SadeepRathnayaka/Turbobot-Autonomous-Robot/turbobot_description/photos/DeskPortraitA_01.jpg

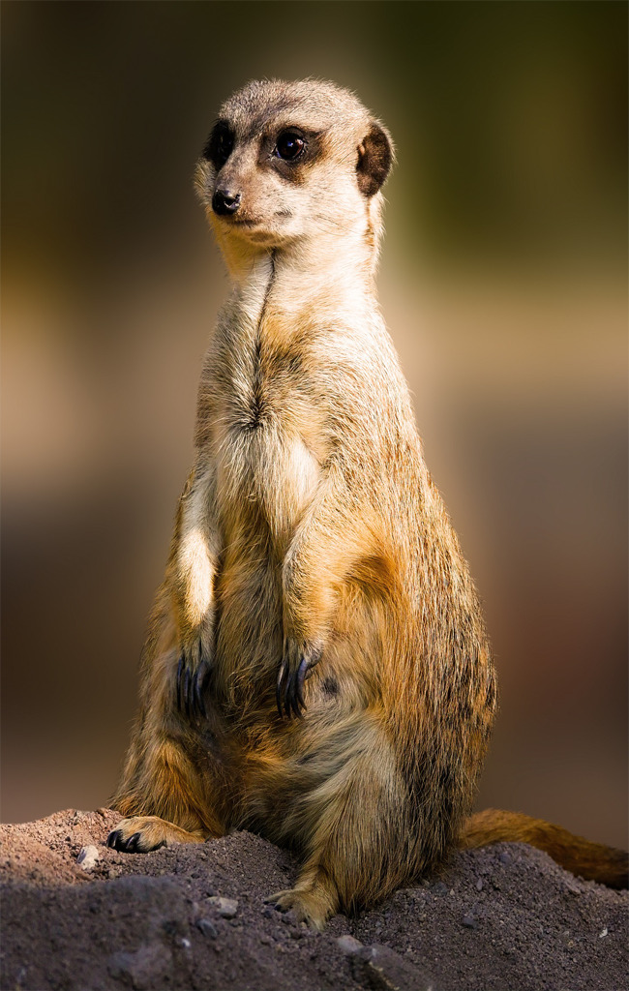
turbobot_description/photos/DeskPortraitA_01.jpg
