SadeepRathnayaka/Turbobot-Autonomous-Robot/turbobot_description/photos/DeskPortraitA_02.jpg

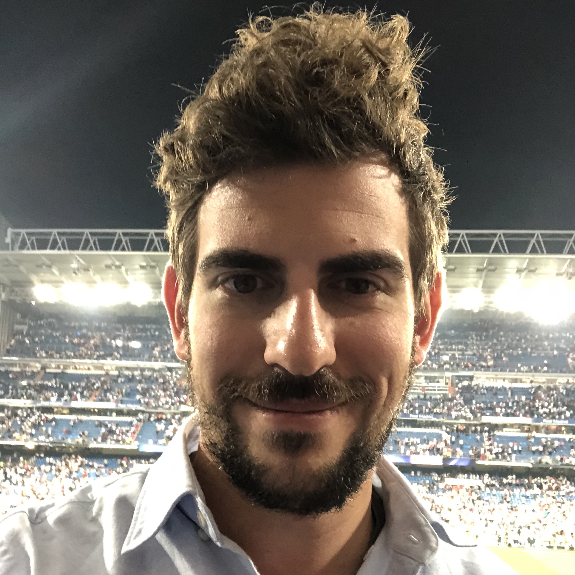
turbobot_description/photos/DeskPortraitA_02.jpg
