SadeepRathnayaka/Turbobot-Autonomous-Robot/turbobot_description/photos/DeskPortraitB_01.jpg

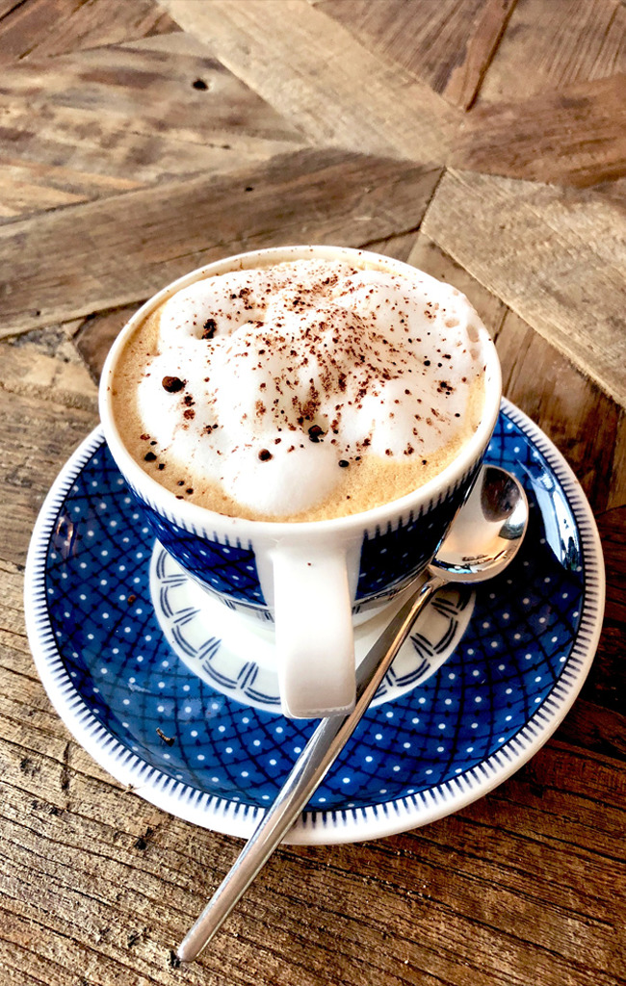
turbobot_description/photos/DeskPortraitB_01.jpg
