SadeepRathnayaka/Turbobot-Autonomous-Robot/turbobot_description/photos/DeskPortraitC_02.jpg

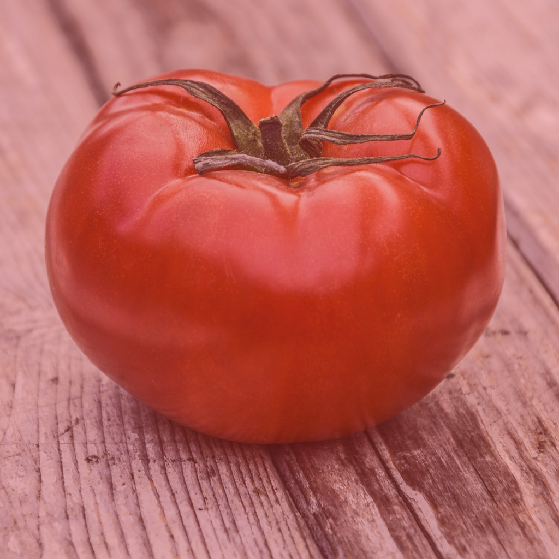
turbobot_description/photos/DeskPortraitC_02.jpg
