SadeepRathnayaka/Turbobot-Autonomous-Robot/turbobot_description/photos/DeskPortraitD_01.jpg

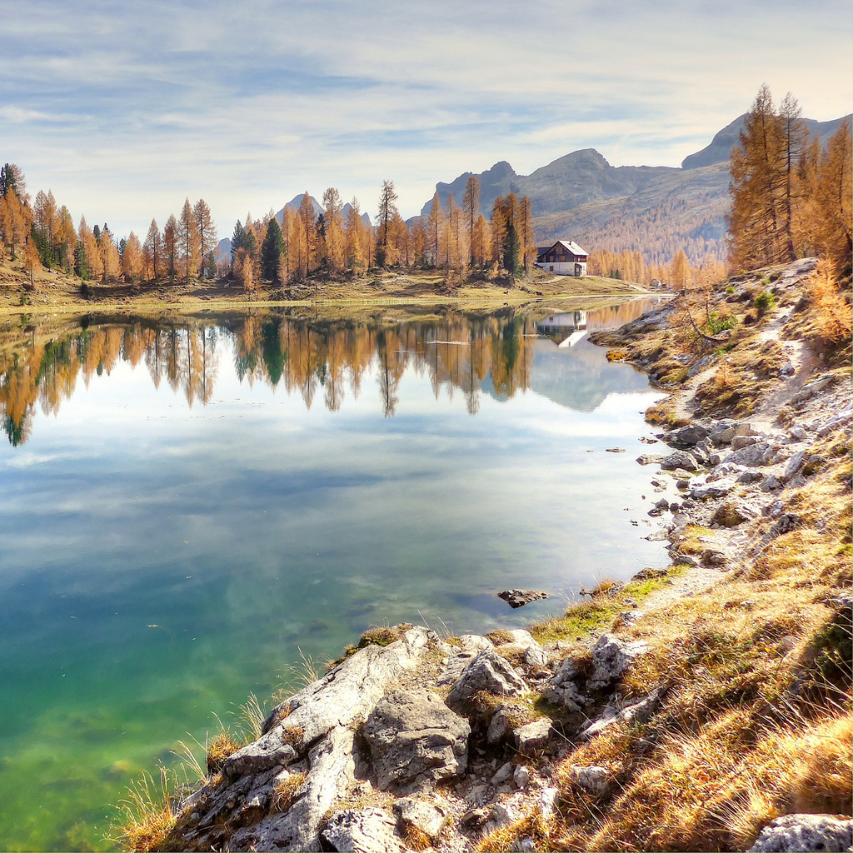
turbobot_description/photos/DeskPortraitD_01.jpg
