SadeepRathnayaka/Turbobot-Autonomous-Robot/turbobot_description/photos/DeskPortraitD_04.jpg

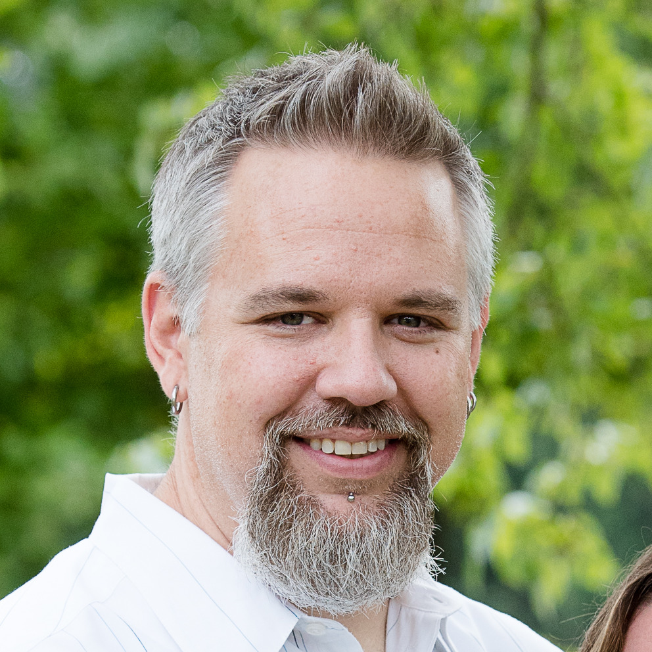
turbobot_description/photos/DeskPortraitD_04.jpg
