SadeepRathnayaka/Turbobot-Autonomous-Robot/turbobot_description/photos/PortraitA_01.jpg

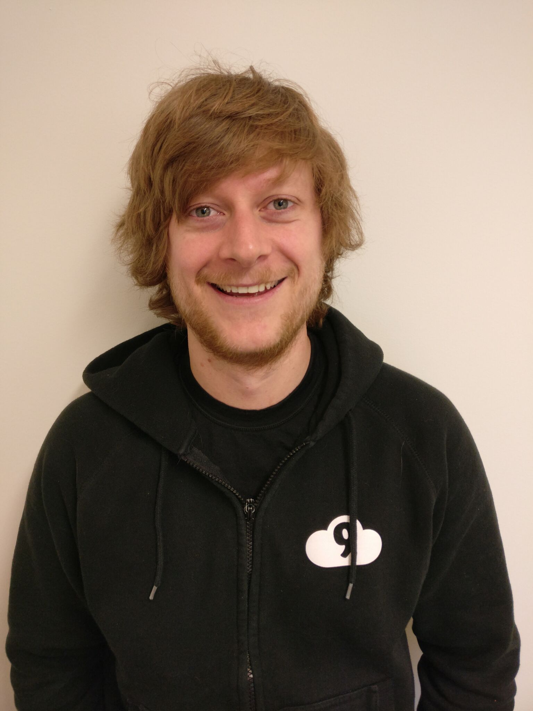
turbobot_description/photos/PortraitA_01.jpg
