SadeepRathnayaka/Turbobot-Autonomous-Robot/turbobot_description/photos/PortraitA_02.jpg

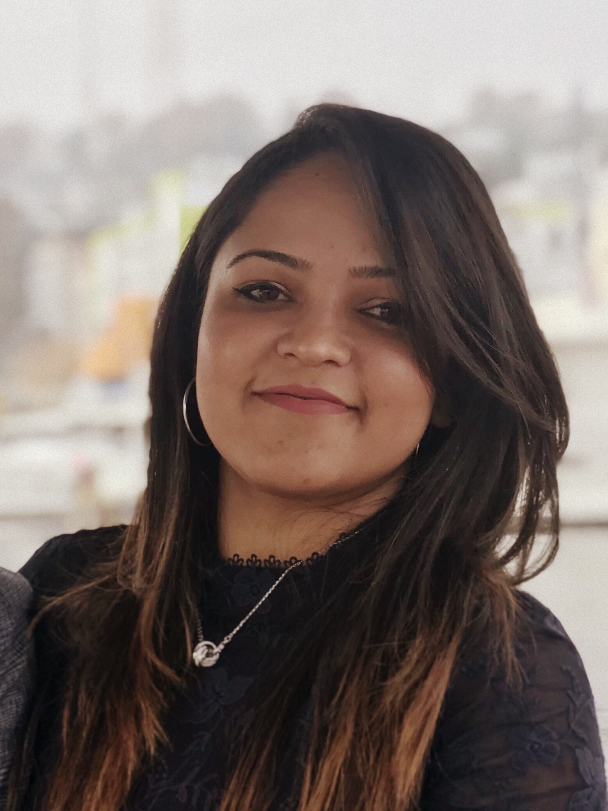
turbobot_description/photos/PortraitA_02.jpg
