SadeepRathnayaka/Turbobot-Autonomous-Robot/turbobot_description/photos/PortraitB_01.jpg

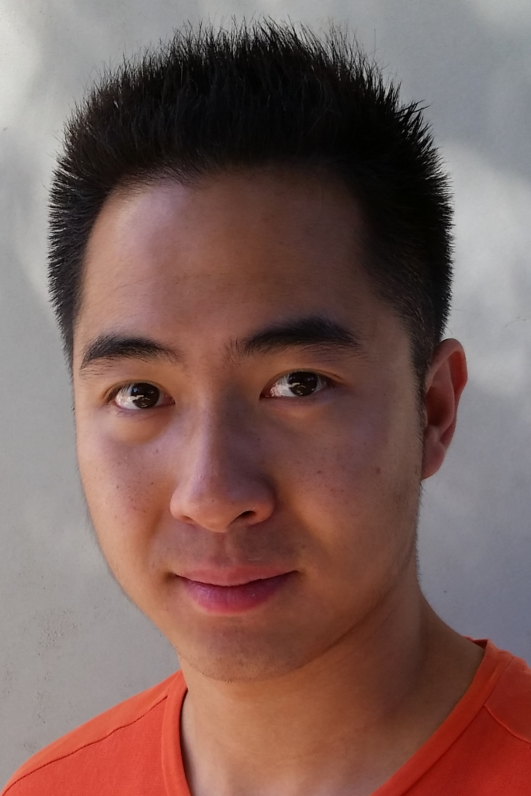
turbobot_description/photos/PortraitB_01.jpg
