SadeepRathnayaka/Turbobot-Autonomous-Robot/turbobot_description/photos/PortraitB_02.jpg

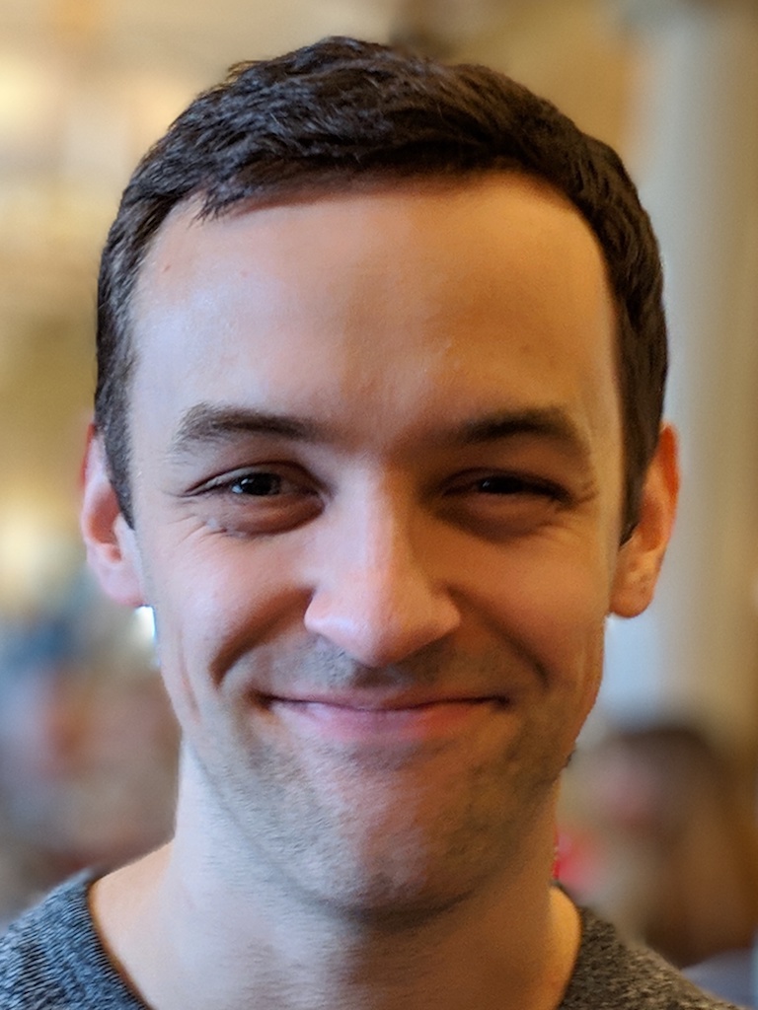
turbobot_description/photos/PortraitB_02.jpg
