SadeepRathnayaka/Turbobot-Autonomous-Robot/turbobot_description/photos/PortraitB_03.jpg

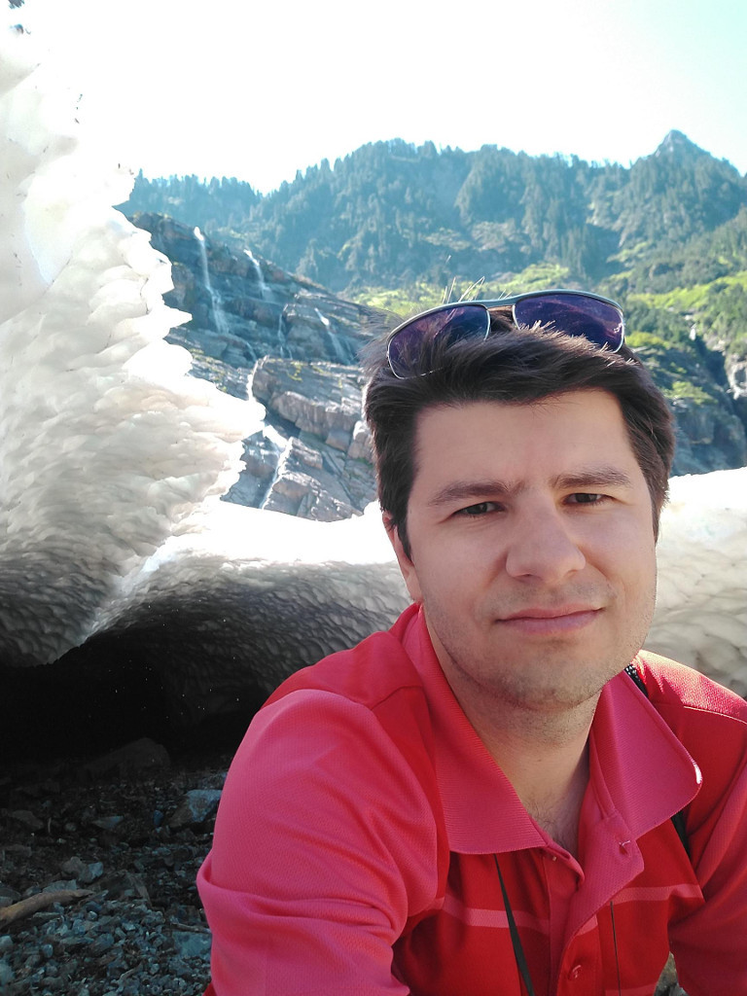
turbobot_description/photos/PortraitB_03.jpg
