SadeepRathnayaka/Turbobot-Autonomous-Robot/turbobot_description/photos/PortraitC_01.jpg

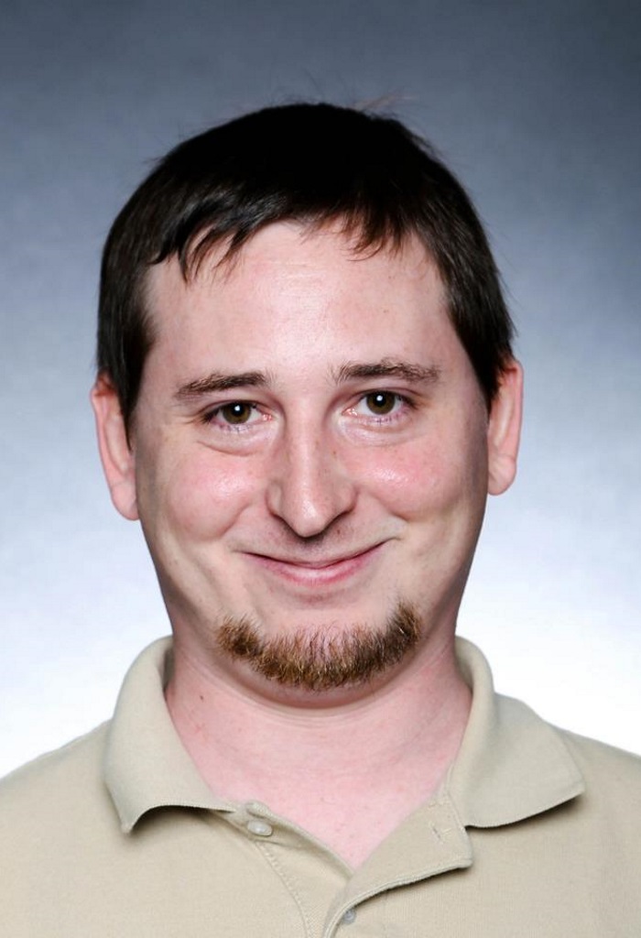
turbobot_description/photos/PortraitC_01.jpg
