SadeepRathnayaka/Turbobot-Autonomous-Robot/turbobot_description/photos/PortraitD_01.jpg

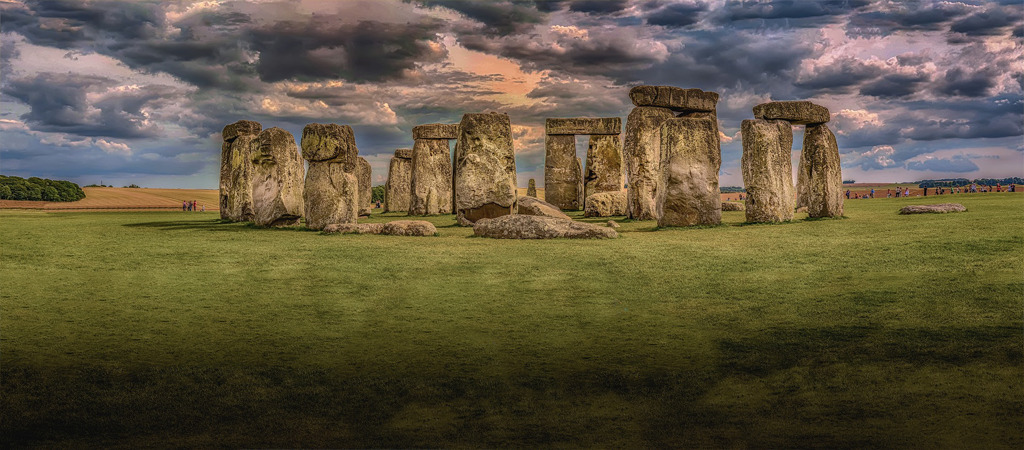
turbobot_description/photos/PortraitD_01.jpg
