SadeepRathnayaka/Turbobot-Autonomous-Robot/turbobot_description/photos/PortraitE_01.jpg

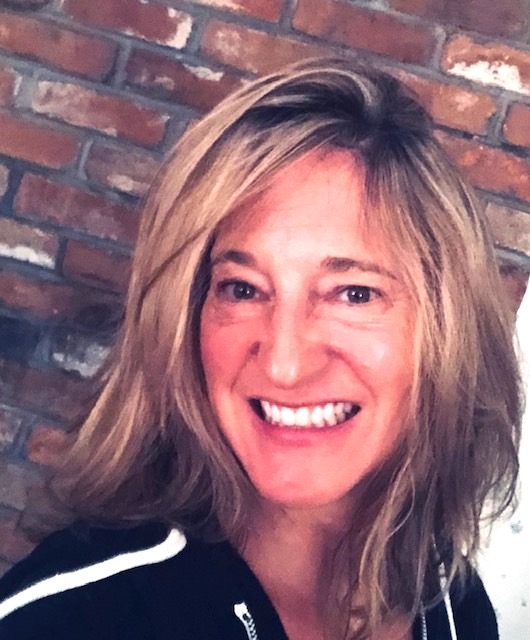
turbobot_description/photos/PortraitE_01.jpg
