SadeepRathnayaka/Turbobot-Autonomous-Robot/turbobot_description/photos/PortraitE_02.jpg

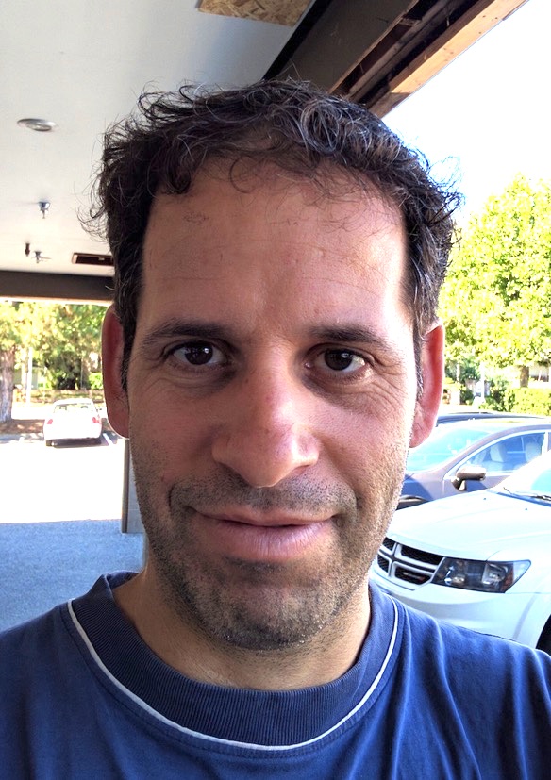
turbobot_description/photos/PortraitE_02.jpg
