SadeepRathnayaka/Turbobot-Autonomous-Robot/turbobot_description/models/aws_robomaker_residential_Ball_01/materials/textures/aws_Ball_01.png

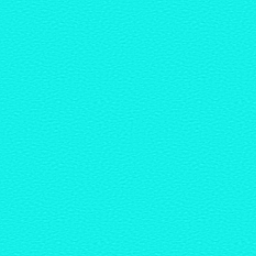
turbobot_description/models/aws_robomaker_residential_Ball_01/materials/textures/aws_Ball_01.png
