SadeepRathnayaka/Turbobot-Autonomous-Robot/turbobot_description/models/aws_robomaker_residential_Bed_01/materials/textures/aws_Bed_01.png

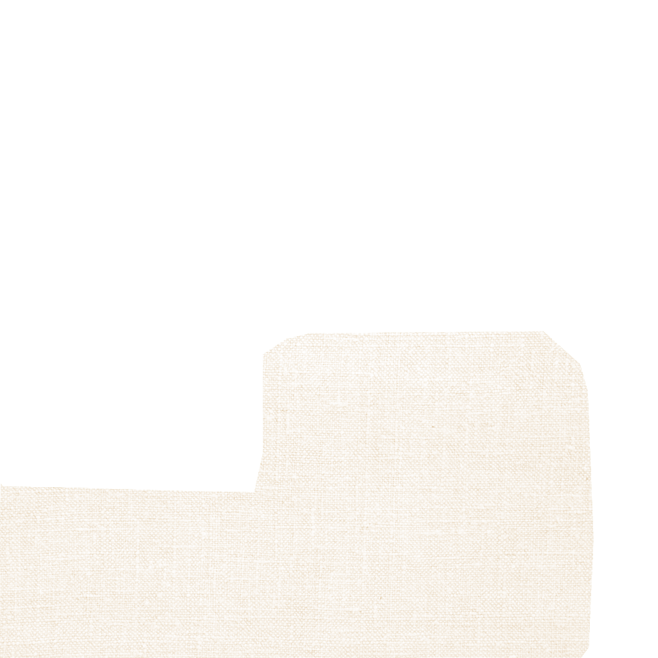
turbobot_description/models/aws_robomaker_residential_Bed_01/materials/textures/aws_Bed_01.png
