SadeepRathnayaka/Turbobot-Autonomous-Robot/turbobot_description/models/aws_robomaker_residential_Board_01/materials/textures/aws_Board_01.png

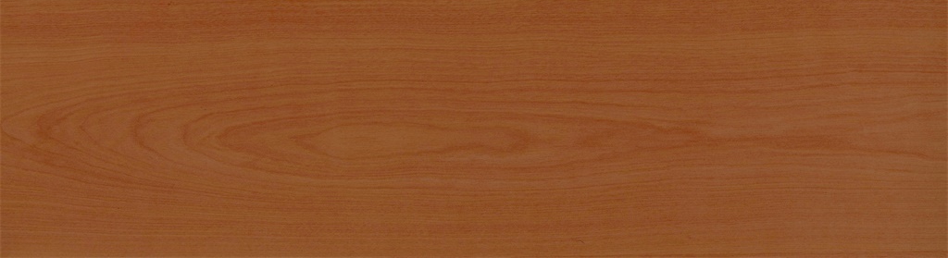
turbobot_description/models/aws_robomaker_residential_Board_01/materials/textures/aws_Board_01.png
