SadeepRathnayaka/Turbobot-Autonomous-Robot/turbobot_description/models/aws_robomaker_residential_ChairA_01/materials/textures/aws_ChairA_01.png

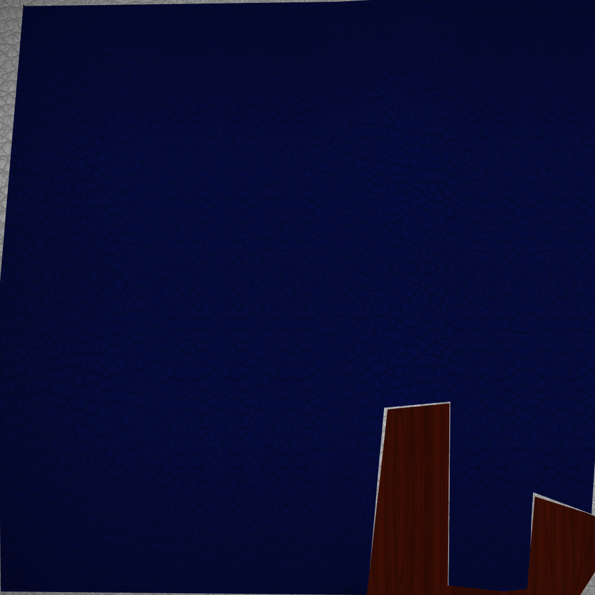
turbobot_description/models/aws_robomaker_residential_ChairA_01/materials/textures/aws_ChairA_01.png
