SadeepRathnayaka/Turbobot-Autonomous-Robot/turbobot_description/models/aws_robomaker_residential_Chandelier_01/materials/textures/aws_Chandelier_01.png

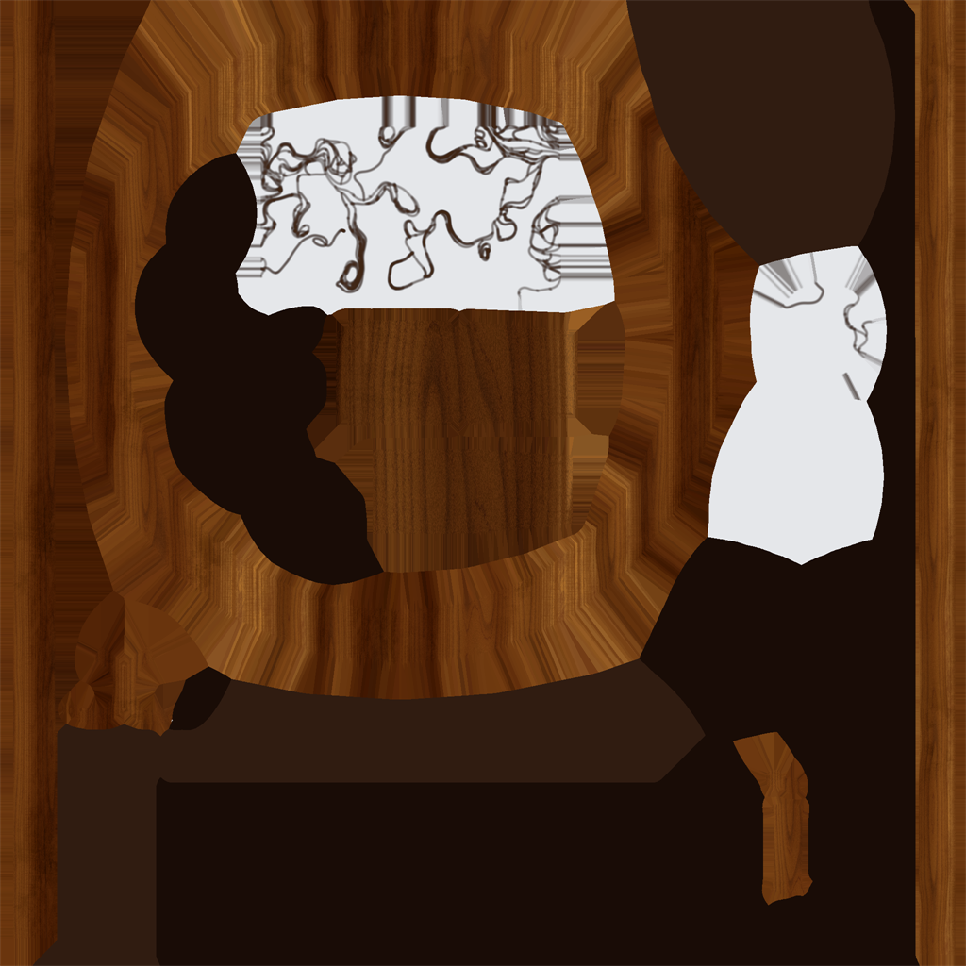
turbobot_description/models/aws_robomaker_residential_Chandelier_01/materials/textures/aws_Chandelier_01.png
