SadeepRathnayaka/Turbobot-Autonomous-Robot/turbobot_description/models/aws_robomaker_residential_CookingBench_01/materials/textures/aws_CookingBench_01.png

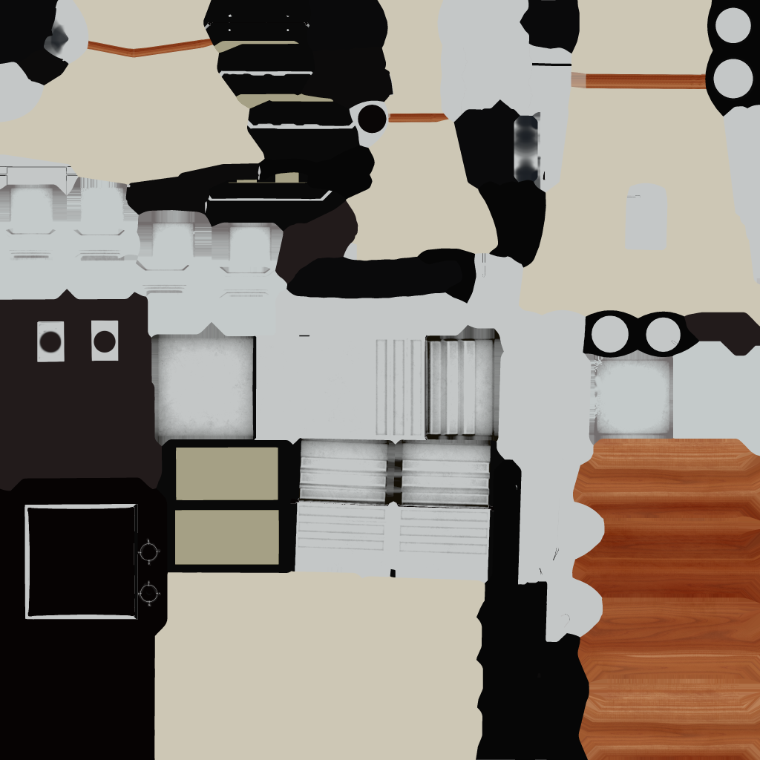
turbobot_description/models/aws_robomaker_residential_CookingBench_01/materials/textures/aws_CookingBench_01.png
