SadeepRathnayaka/Turbobot-Autonomous-Robot/turbobot_description/models/aws_robomaker_residential_Curtain_01/materials/textures/aws_Curtain_01.png

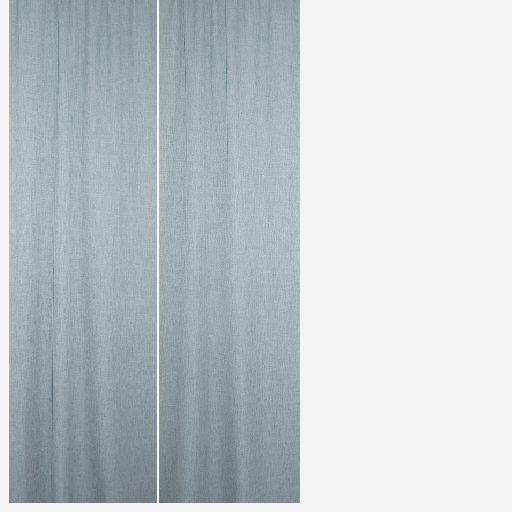
turbobot_description/models/aws_robomaker_residential_Curtain_01/materials/textures/aws_Curtain_01.png
