SadeepRathnayaka/Turbobot-Autonomous-Robot/turbobot_description/models/aws_robomaker_residential_Door_01/materials/textures/aws_Door_01.png

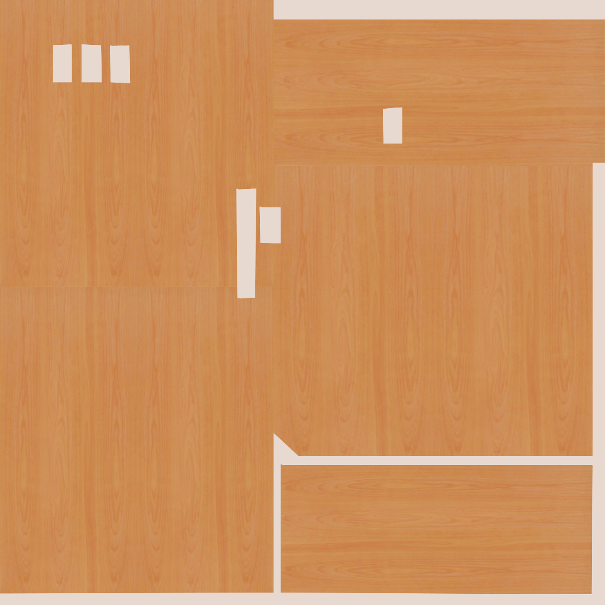
turbobot_description/models/aws_robomaker_residential_Door_01/materials/textures/aws_Door_01.png
