SadeepRathnayaka/Turbobot-Autonomous-Robot/turbobot_description/models/aws_robomaker_residential_FloorB_01/materials/textures/aws_FloorB_01.png

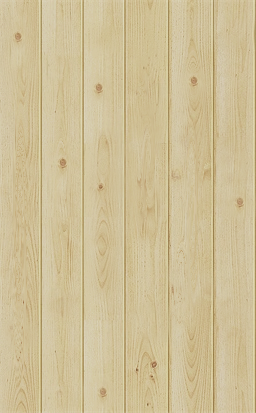
turbobot_description/models/aws_robomaker_residential_FloorB_01/materials/textures/aws_FloorB_01.png
