SadeepRathnayaka/Turbobot-Autonomous-Robot/turbobot_description/models/aws_robomaker_residential_Handle_01/materials/textures/aws_Handle_01.png

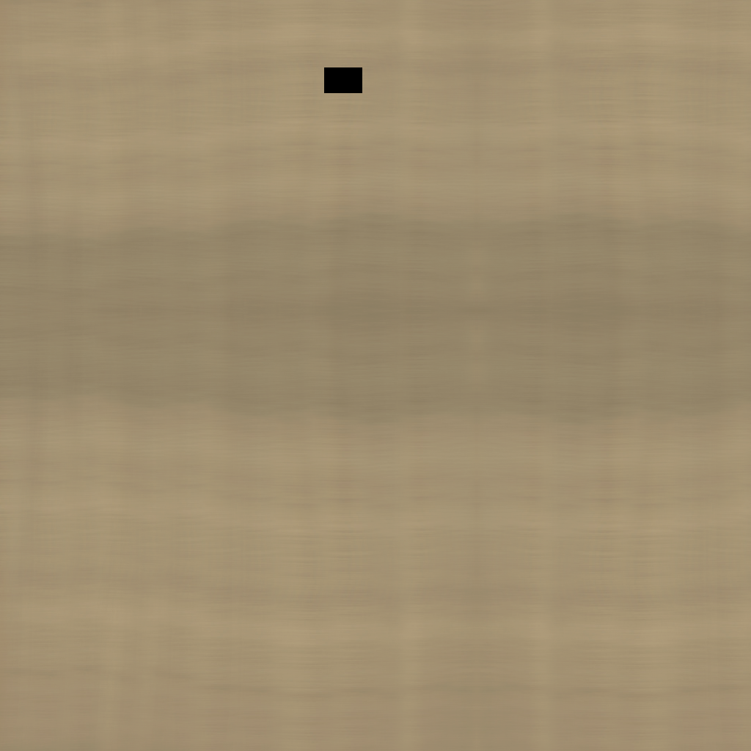
turbobot_description/models/aws_robomaker_residential_Handle_01/materials/textures/aws_Handle_01.png
