SadeepRathnayaka/Turbobot-Autonomous-Robot/turbobot_description/models/aws_robomaker_residential_NightStand_01/materials/textures/aws_NightStand_01.png

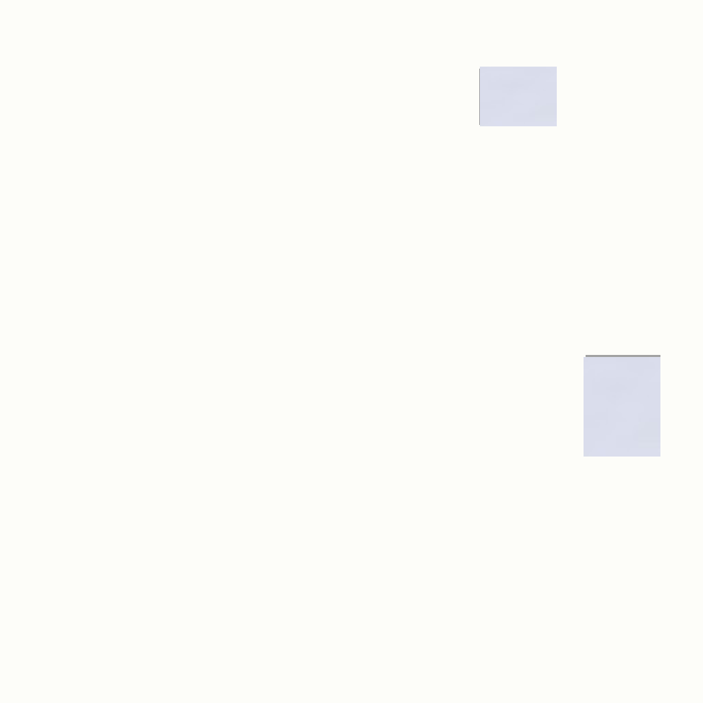
turbobot_description/models/aws_robomaker_residential_NightStand_01/materials/textures/aws_NightStand_01.png
