SadeepRathnayaka/Turbobot-Autonomous-Robot/turbobot_description/models/aws_robomaker_residential_PortraitA_01/materials/textures/aws_PortraitA_02.png

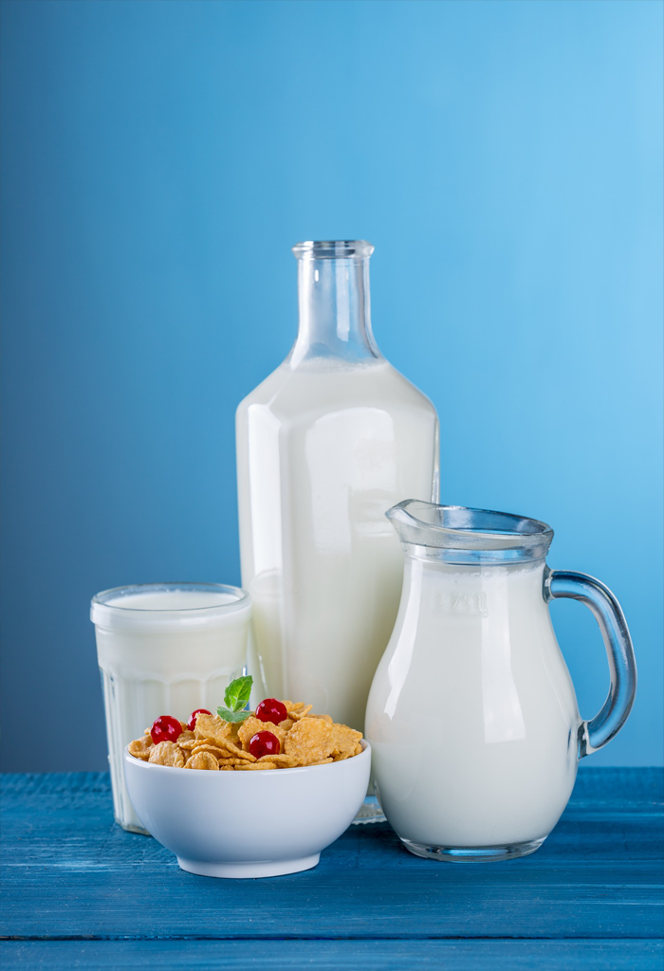
turbobot_description/models/aws_robomaker_residential_PortraitA_01/materials/textures/aws_PortraitA_02.png
