SadeepRathnayaka/Turbobot-Autonomous-Robot/turbobot_description/models/aws_robomaker_residential_PortraitB_01/materials/textures/aws_PortraitB_02.png

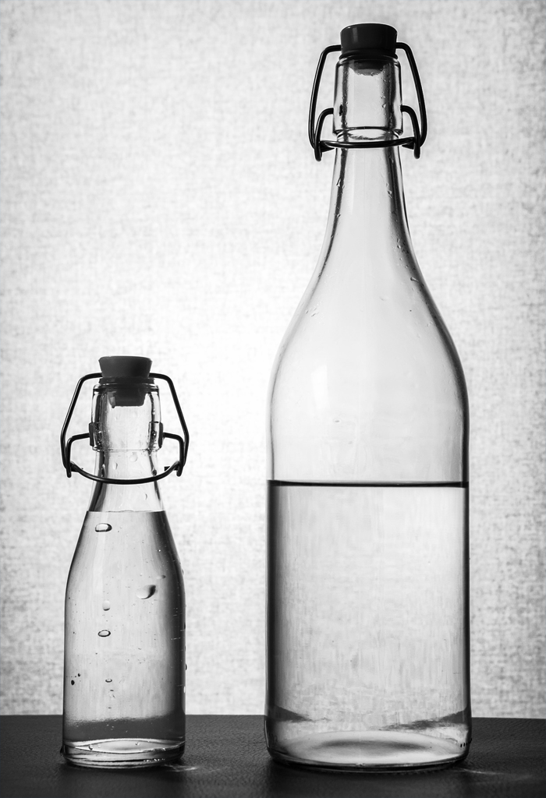
turbobot_description/models/aws_robomaker_residential_PortraitB_01/materials/textures/aws_PortraitB_02.png
