SadeepRathnayaka/Turbobot-Autonomous-Robot/turbobot_description/models/aws_robomaker_residential_PortraitC_01/materials/textures/aws_PortraitC_02.png

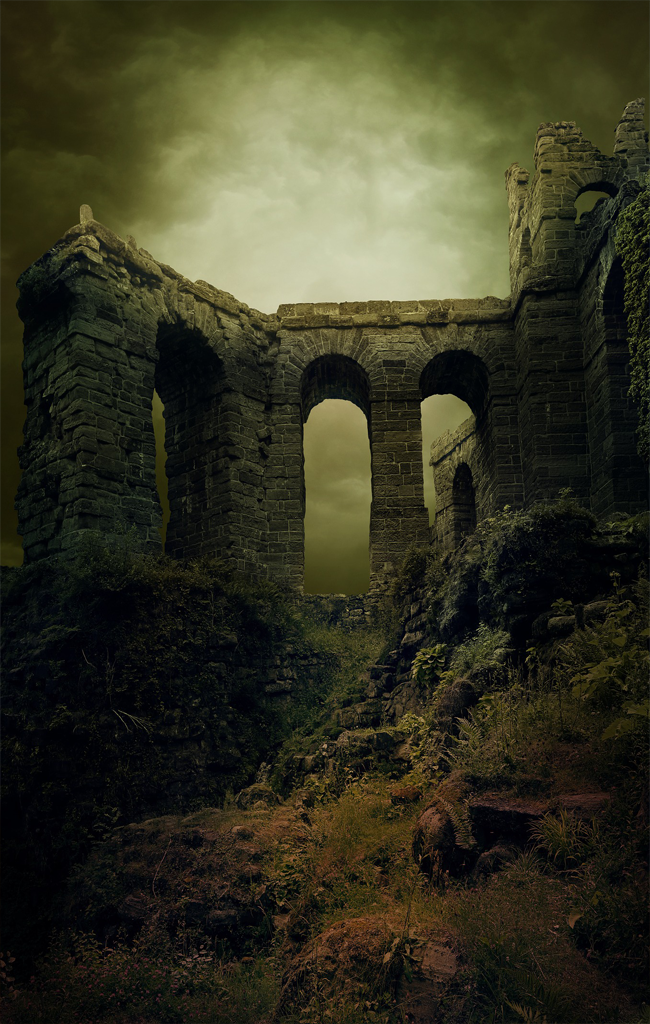
turbobot_description/models/aws_robomaker_residential_PortraitC_01/materials/textures/aws_PortraitC_02.png
