SadeepRathnayaka/Turbobot-Autonomous-Robot/turbobot_description/models/aws_robomaker_residential_PortraitE_01/materials/textures/aws_PortraitE_02.png

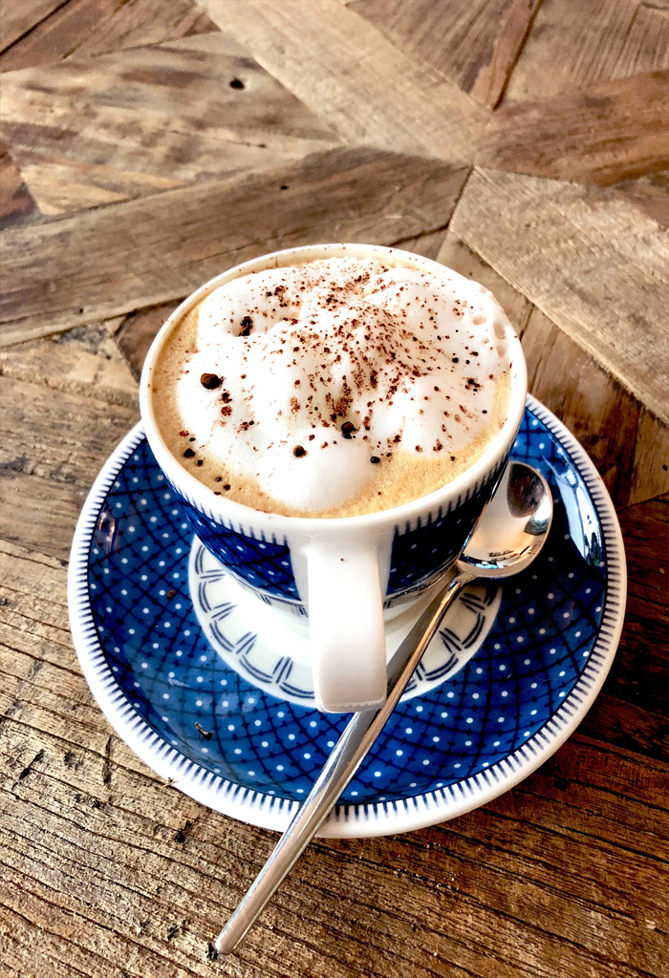
turbobot_description/models/aws_robomaker_residential_PortraitE_01/materials/textures/aws_PortraitE_02.png
