SadeepRathnayaka/Turbobot-Autonomous-Robot/turbobot_description/models/aws_robomaker_residential_Rangehood_01/materials/textures/aws_Rangehood_01.png

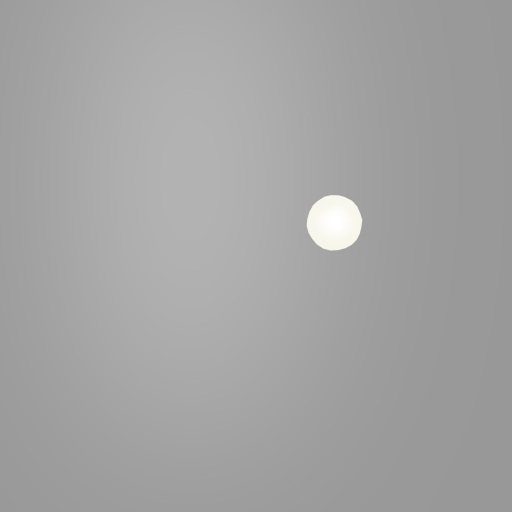
turbobot_description/models/aws_robomaker_residential_Rangehood_01/materials/textures/aws_Rangehood_01.png
