SadeepRathnayaka/Turbobot-Autonomous-Robot/turbobot_description/models/aws_robomaker_residential_RoomWall_01/materials/textures/aws_RoomWall_01.png

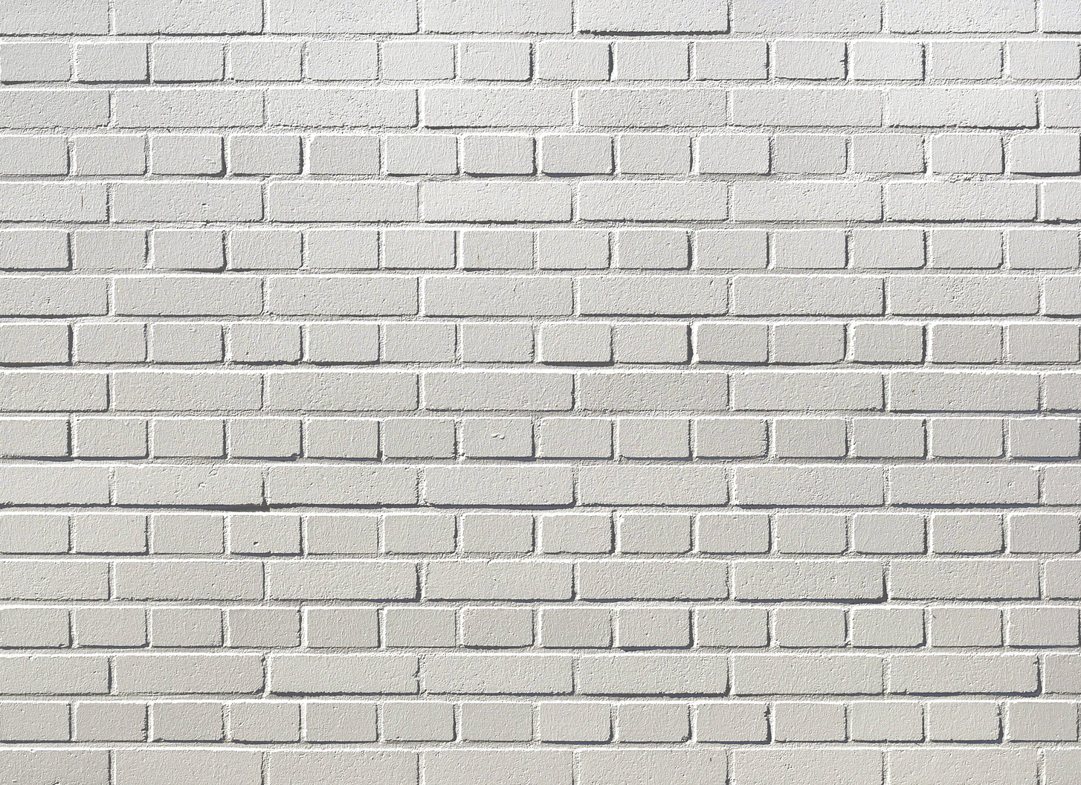
turbobot_description/models/aws_robomaker_residential_RoomWall_01/materials/textures/aws_RoomWall_01.png
