SadeepRathnayaka/Turbobot-Autonomous-Robot/turbobot_description/models/aws_robomaker_residential_Tableware_01/materials/textures/aws_Tableware_01.png

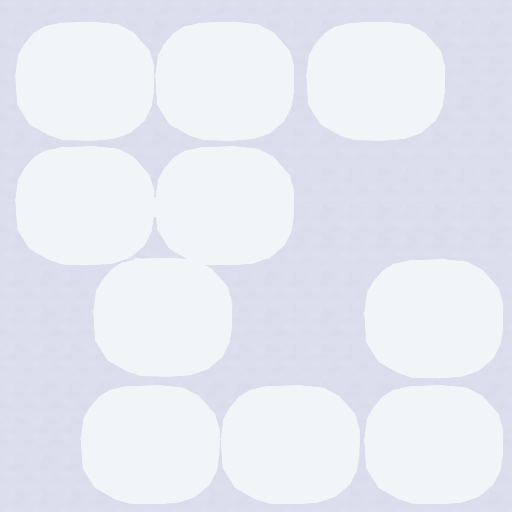
turbobot_description/models/aws_robomaker_residential_Tableware_01/materials/textures/aws_Tableware_01.png
