SadeepRathnayaka/Turbobot-Autonomous-Robot/turbobot_description/models/aws_robomaker_residential_Trash_01/materials/textures/aws_Trash_01.png

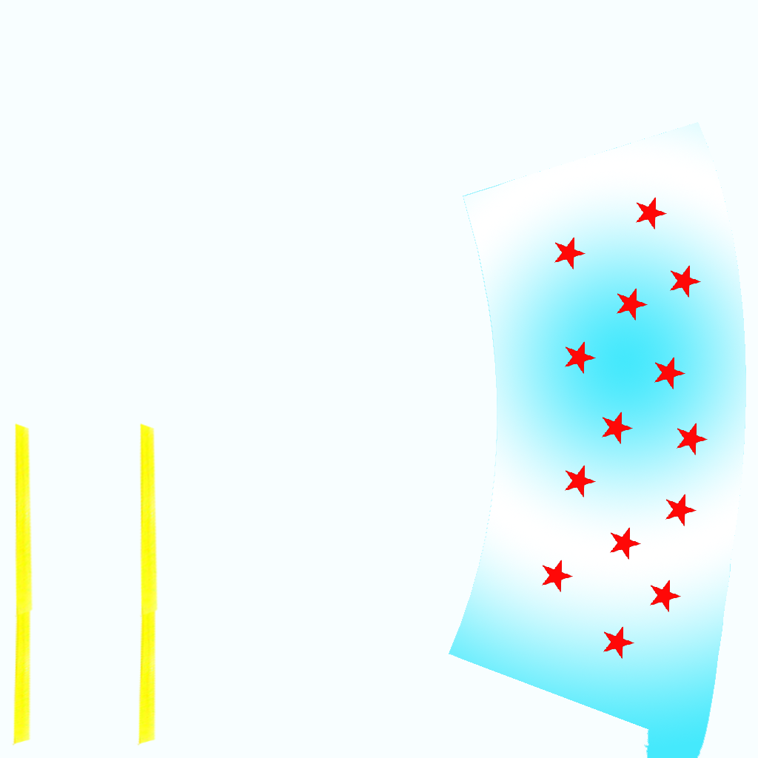
turbobot_description/models/aws_robomaker_residential_Trash_01/materials/textures/aws_Trash_01.png
