SadeepRathnayaka/Turbobot-Autonomous-Robot/turbobot_description/models/aws_robomaker_residential_TV_02/materials/textures/aws_TV_01.png

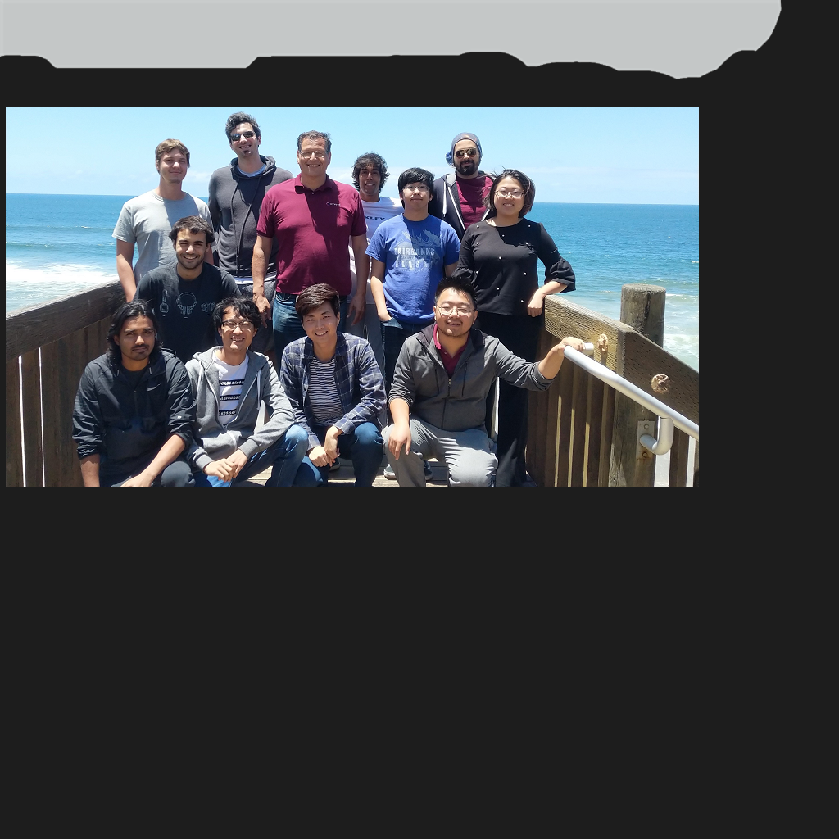
turbobot_description/models/aws_robomaker_residential_TV_02/materials/textures/aws_TV_01.png
