SadeepRathnayaka/Turbobot-Autonomous-Robot/turbobot_description/models/aws_robomaker_residential_Vase_01/materials/textures/aws_Vase_01.png

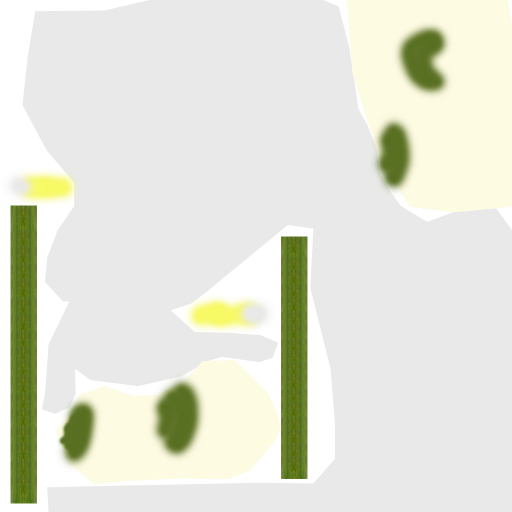
turbobot_description/models/aws_robomaker_residential_Vase_01/materials/textures/aws_Vase_01.png
