SadeepRathnayaka/Turbobot-Autonomous-Robot/turbobot_description/meshes/base_link.STL

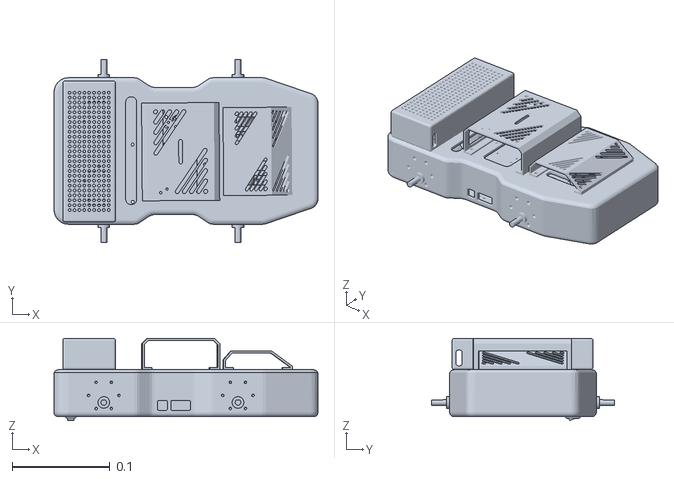
[picture p83: CAD file, 2025-01-22]
turbobot_description/meshes/base_link.STL
0.27 x 0.188 x 0.0841
