SadeepRathnayaka/Turbobot-Autonomous-Robot/CAD Models/Part10_White.STL

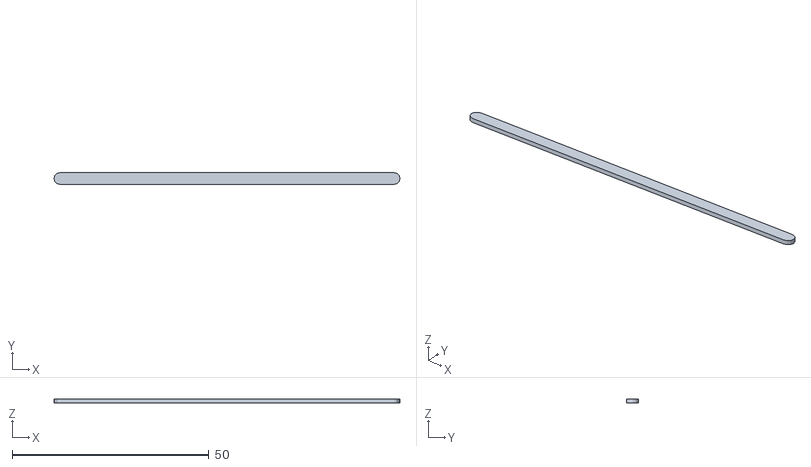
[picture p84: CAD file, 2025-01-28]
CAD Models/Part10_White.STL
88.0 x 3.00 x 1.00
