SadeepRathnayaka/Turbobot-Autonomous-Robot/CAD Models/Solidworks Parts/MPU6050.SLDPRT

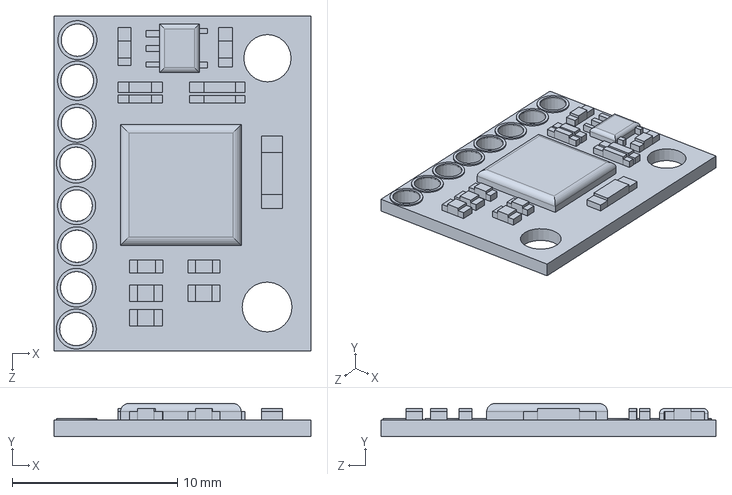
[picture p85: CAD file, 2025-02-02]
CAD Models/Solidworks Parts/MPU6050.SLDPRT
15.6 x 2.00 x 20.3 mm
