SadeepRathnayaka/Turbobot-Autonomous-Robot/turbobot_description/meshes/IMU_link.STL

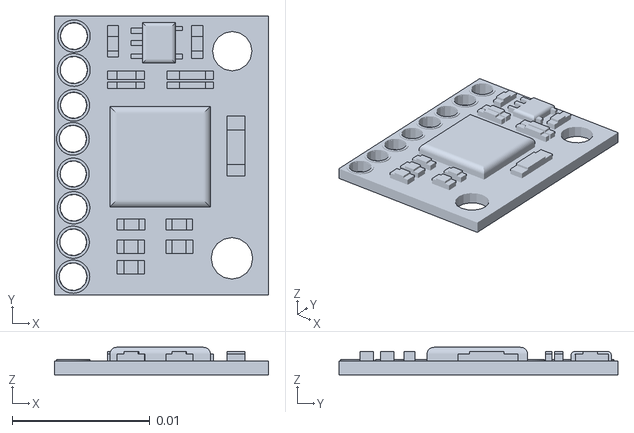
[picture p86: CAD file, 2025-01-22]
turbobot_description/meshes/IMU_link.STL
0.0156 x 0.0203 x 0.002
