SadeepRathnayaka/Turbobot-Autonomous-Robot/CAD Models/Part8.STL

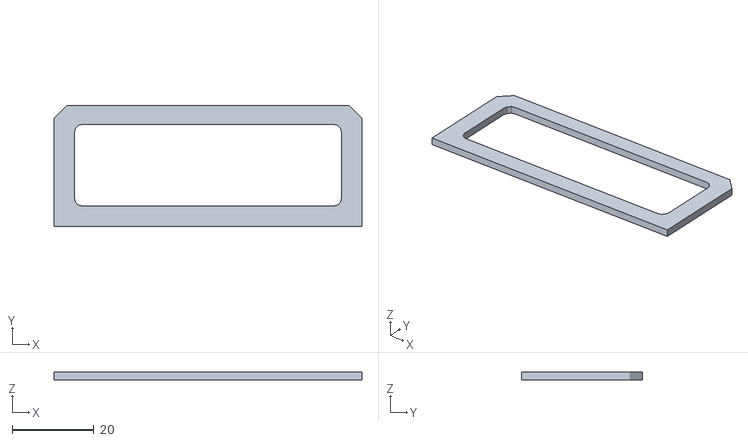
[picture p87: CAD file, 2025-01-28]
CAD Models/Part8.STL
75.2 x 29.6 x 1.90
