SadeepRathnayaka/Turbobot-Autonomous-Robot/CAD Models/Solidworks Parts/Xiaomi Roborock Mi LDS02RR 1st gen LiDAR.SLDPRT

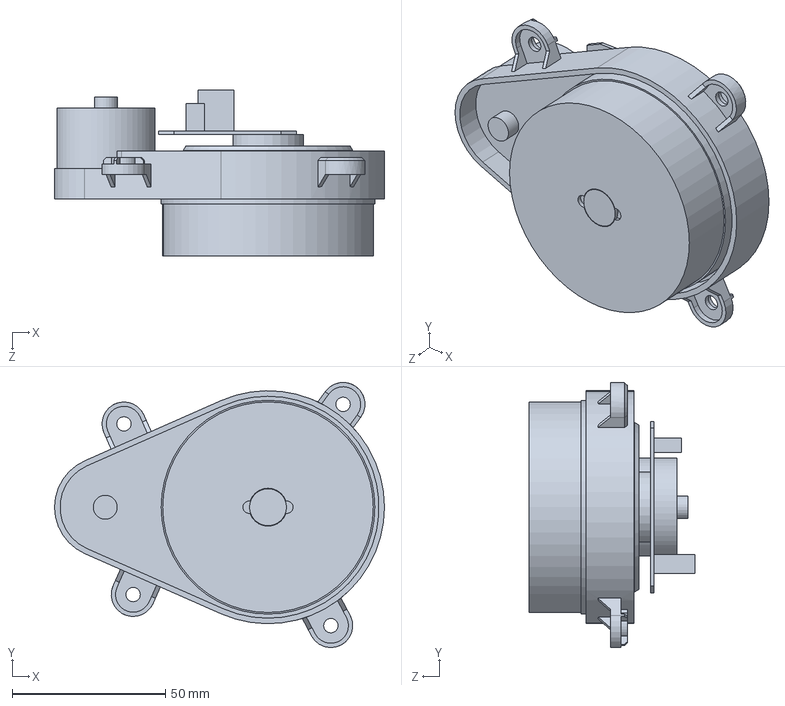
[picture p88: CAD file, 2025-02-02]
CAD Models/Solidworks Parts/Xiaomi Roborock Mi LDS02RR 1st gen LiDAR.SLDPRT
107.7 x 86.5 x 54.1 mm
