SadeepRathnayaka/Turbobot-Autonomous-Robot/CAD Models/Solidworks Parts/Part1.SLDPRT

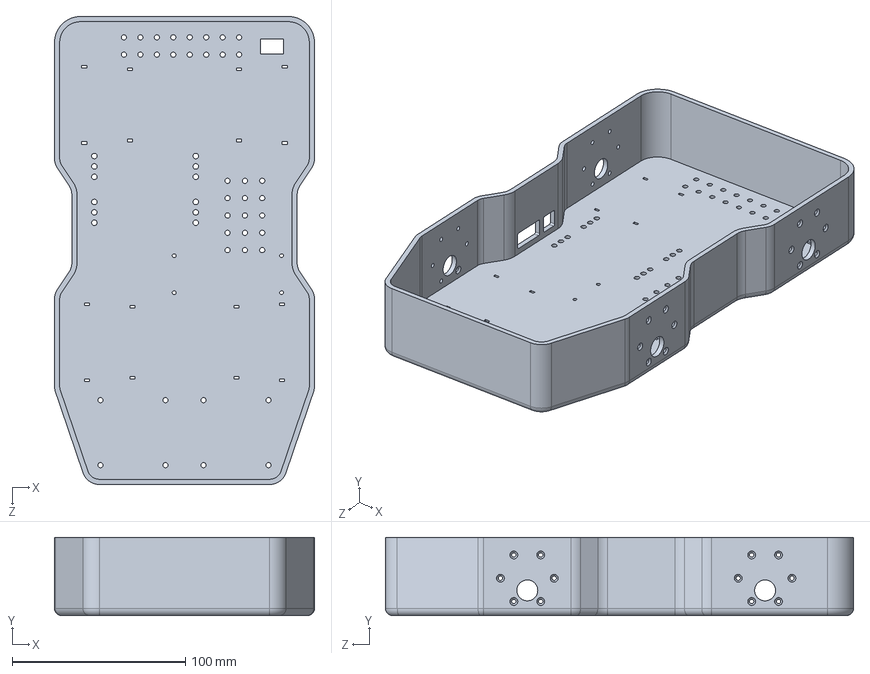
[picture p89: CAD file, 2025-02-02]
CAD Models/Solidworks Parts/Part1.SLDPRT
150.0 x 45.0 x 270.0 mm
